kidmirage/CHESSmate-Reproduction/Firmware/CHESSmate_ESP32/cpu.c

/** CHESSmate emulator for Arduino.
 *
 *  Most of this is the 6502 emulator from Mike Chambers.
 *
 *    http://forum.arduino.cc/index.php?topic=193216.0
 *
 *  Project inspired by Oscar Vermeulen's KIM-1 Uno project.
 *
 *    https://obsolescence.wixsite.com/obsolescence/kim-uno-summary-c1uuh
 *
 *  CHESSmate code added by Michael Gardi.
 *
 *    https://hackaday.io/project/194011-commodore-chessmate-reproduction
 *
 */

#include <stdint.h>

extern uint8_t readRRIOT(uint16_t address);
extern void writeRRIOT(uint16_t address, uint8_t value);
extern void printhex(uint16_t val);
extern void print_instruction(char r_w, uint16_t pc, uint16_t address, uint8_t val);
    

#define NULL (void *) 0

#define CHESSMATE_ROM 0xF000
#define RRIOT_REGISTERS 0x8B00
#define RRIOT_RAM_ADDR 0x8B80
#define RRIOT_ROM_ADDR 0x8C00

#define RAM_SIZE 1536
#define ROM_SIZE 4096
#define RRIOT_REG_SIZE 16
#define RRIOT_RAM_SIZE 64
#define RRIOT_ROM_SIZE 1024

//6502 defines
#define UNDOCUMENTED //when this is defined, undocumented opcodes are handled.
                     //otherwise, they're simply treated as NOPs.

#define USE_TIMING //slower, but allows you to specify number of cycles to run for exec6502
                   //rather than simply a number of instructions. also uses a little more
                   //program memory when enabled.

#define FLAG_CARRY     0x01
#define FLAG_ZERO      0x02
#define FLAG_INTERRUPT 0x04
#define FLAG_DECIMAL   0x08
#define FLAG_BREAK     0x10
#define FLAG_CONSTANT  0x20
#define FLAG_OVERFLOW  0x40
#define FLAG_SIGN      0x80

#define BASE_STACK     0x100

#define saveaccum(n) a = (uint8_t)((n) & 0x00FF)


//flag modifier macros
#define setcarry() cpustatus |= FLAG_CARRY
#define clearcarry() cpustatus &= (~FLAG_CARRY)
#define setzero() cpustatus |= FLAG_ZERO
#define clearzero() cpustatus &= (~FLAG_ZERO)
#define setinterrupt() cpustatus |= FLAG_INTERRUPT
#define clearinterrupt() cpustatus &= (~FLAG_INTERRUPT)
#define setdecimal() cpustatus |= FLAG_DECIMAL
#define cleardecimal() cpustatus &= (~FLAG_DECIMAL)
#define setoverflow() cpustatus |= FLAG_OVERFLOW
#define clearoverflow() cpustatus &= (~FLAG_OVERFLOW)
#define setsign() cpustatus |= FLAG_SIGN
#define clearsign() cpustatus &= (~FLAG_SIGN)


//flag calculation macros
#define zerocalc(n) { if ((n) & 0x00FF) clearzero(); else setzero(); }

#define signcalc(n) { if ((n) & 0x0080) setsign(); else clearsign(); }

#define carrycalc(n) { if ((n) & 0xFF00) setcarry(); else clearcarry(); }

#define overflowcalc(n, m, o) { if (((n) ^ (uint16_t)(m)) & ((n) ^ (o)) & 0x0080) setoverflow(); else clearoverflow(); }


//6502 CPU registers
uint16_t pc;
uint8_t sp, a, x, y, cpustatus;
// BCD fix OV 20140915 - helper variables for adc and sbc
uint16_t lxx,hxx;
// end of BCD fix part 1


//helper variables
uint32_t instructions = 0; //keep track of total instructions executed
int32_t clockticks6502 = 0, clockgoal6502 = 0;
uint16_t oldpc, ea, reladdr, value, result;
uint8_t opcode, oldcpustatus, useaccum;

uint16_t getpc() {
  return(pc);
}

uint8_t getop() {
  return(opcode);
}

uint8_t RAM[RAM_SIZE];

uint8_t const CHESSMATE[ROM_SIZE] = {
  0xd8, 0x58, 0xa2, 0xfe, 0x9a, 0xa9, 0x3f, 0x8d, 0x03, 0x8b, 0xa9, 0xff, 0xa2, 0x00, 0x95, 0x00,
  0xd5, 0x00, 0xf0, 0x05, 0xb5, 0x00, 0x4c, 0x14, 0xf0, 0xca, 0xd0, 0xf2, 0x49, 0xff, 0xf0, 0xee,
  0xa9, 0x05, 0x85, 0x53, 0xa2, 0x21, 0xbd, 0x52, 0xfe, 0x95, 0x00, 0xca, 0x10, 0xf8, 0x86, 0x59,
  0x20, 0xf0, 0xf2, 0xa9, 0x70, 0x85, 0x56, 0xa9, 0x20, 0x20, 0x9c, 0xff, 0x38, 0xe9, 0x04, 0xd0,
  0xf8, 0xa2, 0x04, 0x4c, 0x60, 0xf2, 0xa9, 0xee, 0x85, 0x83, 0x85, 0x84, 0xd8, 0xa2, 0xfe, 0x9a,
  0xa2, 0xb8, 0x86, 0x61, 0xa5, 0x78, 0x29, 0x88, 0x24, 0x56, 0x70, 0x02, 0x09, 0x10, 0x85, 0x78,
  0xa2, 0x00, 0x38, 0x20, 0x04, 0xff, 0xc9, 0x0a, 0xd0, 0x03, 0x4c, 0xb9, 0xf0, 0xc9, 0x09, 0xf0,
  0xd5, 0xe0, 0x04, 0x30, 0x02, 0xa2, 0x00, 0xe0, 0x00, 0xd0, 0x04, 0x86, 0x83, 0x86, 0x84, 0x20,
  0x85, 0xf0, 0x4c, 0x62, 0xf0, 0xe0, 0x03, 0xf0, 0x16, 0xe0, 0x02, 0xf0, 0x0e, 0xe0, 0x01, 0xf0,
  0x04, 0x0a, 0x0a, 0x0a, 0x0a, 0x05, 0x83, 0x85, 0x83, 0xe8, 0x60, 0x0a, 0x0a, 0x0a, 0x0a, 0x05,
  0x84, 0x85, 0x84, 0xe8, 0x60, 0xa9, 0x00, 0x85, 0x7c, 0x85, 0x7d, 0x85, 0x7e, 0xa9, 0xf5, 0x8d,
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
	  return (CHESSMATE[PGMaddr]);
  }

  // RAM memory.
  if (address < RAM_SIZE) return(RAM[address]);

  // Check for RRIOT registers.
  if (address >= RRIOT_REGISTERS && address < (RRIOT_REGISTERS + RRIOT_REG_SIZE)) {
	  PGMaddr = address - RRIOT_REGISTERS;
	  return readRRIOT(PGMaddr);
  }

  // Check for RRIOT RAM.
  if (address >= RRIOT_RAM_ADDR && address < (RRIOT_RAM_ADDR + RRIOT_RAM_SIZE)) {
	  PGMaddr = address - RRIOT_RAM_ADDR;
  	return(RRIOT_RAM[PGMaddr]);
  }

  // Check for OPENING_BOOK.
  if (address >= RRIOT_ROM_ADDR && address < (RRIOT_ROM_ADDR + RRIOT_ROM_SIZE)) {
    PGMaddr = address - RRIOT_ROM_ADDR;
    return(OPENING_BOOK[PGMaddr]);
  }

  // Should have no effect on the program.
  if (address == 0x8009) {
    return 0x00;
  }

  // Catch any unhandled reads.
  uint16_t showpc = getpc();
  print_instruction('r',showpc,address,0);
  return 0xFF;
}

void write6502(uint16_t address, uint8_t value) {
  uint16_t PGMaddr;

  if (address < RAM_SIZE) {
    RAM[address] = value;
    return;
  }

  // Check for RRIOT registers.
  if (address >= RRIOT_REGISTERS && address < (RRIOT_REGISTERS + RRIOT_REG_SIZE)) {
	  PGMaddr = address - RRIOT_REGISTERS;
	  writeRRIOT(PGMaddr, value);
    return;
  }

  // Check for RRIOT RAM.
  if (address >= RRIOT_RAM_ADDR && address < (RRIOT_RAM_ADDR + RRIOT_RAM_SIZE)) {
  	  PGMaddr = address - RRIOT_RAM_ADDR;
      RRIOT_RAM[PGMaddr] = value;
      return;
  }
  // Catch any unhandled writes.
  uint16_t showpc = getpc();
  print_instruction('w',showpc,address, value);
}

//a few general functions used by various other functions
void push16(uint16_t pushval) {
    write6502(BASE_STACK + sp, (pushval >> 8) & 0xFF);
    write6502(BASE_STACK + ((sp - 1) & 0xFF), pushval & 0xFF);
    sp -= 2;
}

void push8(uint8_t pushval) {
    write6502(BASE_STACK + sp--, pushval);
}

uint16_t pull16() {
    uint16_t temp16;
    temp16 = read6502(BASE_STACK + ((sp + 1) & 0xFF)) | ((uint16_t)read6502(BASE_STACK + ((sp + 2) & 0xFF)) << 8);
    sp += 2;
    return(temp16);
}

uint8_t pull8() {
    return (read6502(BASE_STACK + ++sp));
}

void reset6502() {
    pc = (uint16_t)read6502(0xFFFC) | ((uint16_t)read6502(0xFFFD) << 8);
    a = 0;
    x = 0;
    y = 0;
    sp = 0xFD;
    cpustatus |= FLAG_CONSTANT;
}

//addressing mode functions, calculates effective addresses
void imp() { //implied
}

void acc() { //accumulator
  useaccum = 1;
}

void imm() { //immediate
    ea = pc++;
}

void zp() { //zero-page
    ea = (uint16_t)read6502((uint16_t)pc++);
}

void zpx() { //zero-page,X
    ea = ((uint16_t)read6502((uint16_t)pc++) + (uint16_t)x) & 0xFF; //zero-page wraparound
}

void zpy() { //zero-page,Y
    ea = ((uint16_t)read6502((uint16_t)pc++) + (uint16_t)y) & 0xFF; //zero-page wraparound
}

void rel() { //relative for branch ops (8-bit immediate value, sign-extended)
    reladdr = (uint16_t)read6502(pc++);
    if (reladdr & 0x80) reladdr |= 0xFF00;
}

void abso() { //absolute
    ea = (uint16_t)read6502(pc) | ((uint16_t)read6502(pc+1) << 8);
    pc += 2;
}

void absx() { //absolute,X
    uint16_t startpage;
    ea = ((uint16_t)read6502(pc) | ((uint16_t)read6502(pc+1) << 8));
    startpage = ea & 0xFF00;
    ea += (uint16_t)x;

    pc += 2;
}

void absy() { //absolute,Y
    uint16_t startpage;
    ea = ((uint16_t)read6502(pc) | ((uint16_t)read6502(pc+1) << 8));
    startpage = ea & 0xFF00;
    ea += (uint16_t)y;

    pc += 2;
}

void ind() { //indirect
    uint16_t eahelp, eahelp2;
    eahelp = (uint16_t)read6502(pc) | (uint16_t)((uint16_t)read6502(pc+1) << 8);
    eahelp2 = (eahelp & 0xFF00) | ((eahelp + 1) & 0x00FF); //replicate 6502 page-boundary wraparound bug
    ea = (uint16_t)read6502(eahelp) | ((uint16_t)read6502(eahelp2) << 8);
    pc += 2;
}

void indx() { // (indirect,X)
    uint16_t eahelp;
    eahelp = (uint16_t)(((uint16_t)read6502(pc++) + (uint16_t)x) & 0xFF); //zero-page wraparound for table pointer
    ea = (uint16_t)read6502(eahelp & 0x00FF) | ((uint16_t)read6502((eahelp+1) & 0x00FF) << 8);
}

void indy() { // (indirect),Y
    uint16_t eahelp, eahelp2, startpage;
    eahelp = (uint16_t)read6502(pc++);
    eahelp2 = (eahelp & 0xFF00) | ((eahelp + 1) & 0x00FF); //zero-page wraparound
    ea = (uint16_t)read6502(eahelp) | ((uint16_t)read6502(eahelp2) << 8);
    startpage = ea & 0xFF00;
    ea += (uint16_t)y;

}

static uint16_t getvalue() {
    if (useaccum) return((uint16_t)a);
        else return((uint16_t)read6502(ea));
}

static uint16_t getvalue16() {
    return((uint16_t)read6502(ea) | ((uint16_t)read6502(ea+1) << 8));
}

void putvalue(uint16_t saveval) {
    if (useaccum) a = (uint8_t)(saveval & 0x00FF);
        else write6502(ea, (saveval & 0x00FF));
}


//instruction handler functions
void adc() {
    // penaltyop = 1;
    value = getvalue();
    result = (uint16_t)a + value + (uint16_t)(cpustatus & FLAG_CARRY);

    zerocalc(result);
    overflowcalc(result, a, value);
    signcalc(result);

    #ifndef NES_CPU
    if (cpustatus & FLAG_DECIMAL)       /* detect and apply BCD nybble carries */
        result += ((((result + 0x66) ^ (uint16_t)a ^ value) >> 3) & 0x22) * 3;
    #endif

    carrycalc(result);
    saveaccum(result);

    saveaccum(result);
}

void op_and() {
    value = getvalue();
    result = (uint16_t)a & value;

    zerocalc(result);
    signcalc(result);

    saveaccum(result);
}

void asl() {
    value = getvalue();
    result = value << 1;

    carrycalc(result);
    zerocalc(result);
    signcalc(result);

    putvalue(result);
}

void bcc() {
    if ((cpustatus & FLAG_CARRY) == 0) {
        oldpc = pc;
        pc += reladdr;
        if ((oldpc & 0xFF00) != (pc & 0xFF00)) clockticks6502 += 2; //check if jump crossed a page boundary
            else clockticks6502++;
    }
}

void bcs() {
    if ((cpustatus & FLAG_CARRY) == FLAG_CARRY) {
        oldpc = pc;
        pc += reladdr;
        if ((oldpc & 0xFF00) != (pc & 0xFF00)) clockticks6502 += 2; //check if jump crossed a page boundary
            else clockticks6502++;
    }
}

void beq() {
    if ((cpustatus & FLAG_ZERO) == FLAG_ZERO) {
        oldpc = pc;
        pc += reladdr;
        if ((oldpc & 0xFF00) != (pc & 0xFF00)) clockticks6502 += 2; //check if jump crossed a page boundary
            else clockticks6502++;
    }
}

void op_bit() {
    value = getvalue();
    result = (uint16_t)a & value;

    zerocalc(result);
    cpustatus = (cpustatus & 0x3F) | (uint8_t)(value & 0xC0);
}

void bmi() {
    if ((cpustatus & FLAG_SIGN) == FLAG_SIGN) {
        oldpc = pc;
        pc += reladdr;
        if ((oldpc & 0xFF00) != (pc & 0xFF00)) clockticks6502 += 2; //check if jump crossed a page boundary
            else clockticks6502++;
    }
}

void bne() {
    if ((cpustatus & FLAG_ZERO) == 0) {
        oldpc = pc;
        pc += reladdr;
        if ((oldpc & 0xFF00) != (pc & 0xFF00)) clockticks6502 += 2; //check if jump crossed a page boundary
            else clockticks6502++;
    }
}

void bpl() {
    if ((cpustatus & FLAG_SIGN) == 0) {
        oldpc = pc;
        pc += reladdr;
        if ((oldpc & 0xFF00) != (pc & 0xFF00)) clockticks6502 += 2; //check if jump crossed a page boundary
            else clockticks6502++;
    }
}

void brk() {
    pc++;
    push16(pc); //push next instruction address onto stack
    push8(cpustatus | FLAG_BREAK); //push CPU cpustatus to stack
    setinterrupt(); //set interrupt flag
    pc = (uint16_t)read6502(0xFFFE) | ((uint16_t)read6502(0xFFFF) << 8);
}

void bvc() {
    if ((cpustatus & FLAG_OVERFLOW) == 0) {
        oldpc = pc;
        pc += reladdr;
        if ((oldpc & 0xFF00) != (pc & 0xFF00)) clockticks6502 += 2; //check if jump crossed a page boundary
            else clockticks6502++;
    }
}

void bvs() {
    if ((cpustatus & FLAG_OVERFLOW) == FLAG_OVERFLOW) {
        oldpc = pc;
        pc += reladdr;
        if ((oldpc & 0xFF00) != (pc & 0xFF00)) clockticks6502 += 2; //check if jump crossed a page boundary
            else clockticks6502++;
    }
}

void clc() {
    clearcarry();
}

void cld() {
    cleardecimal();
}

void cli() {
    clearinterrupt();
}

void clv() {
    clearoverflow();
}

void cmp() {
    value = getvalue();
    result = (uint16_t)a - value;

    if (a >= (uint8_t)(value & 0x00FF)) setcarry();
        else clearcarry();
    if (a == (uint8_t)(value & 0x00FF)) setzero();
        else clearzero();
    signcalc(result);
}

void cpx() {
    value = getvalue();
    result = (uint16_t)x - value;

    if (x >= (uint8_t)(value & 0x00FF)) setcarry();
        else clearcarry();
    if (x == (uint8_t)(value & 0x00FF)) setzero();
        else clearzero();
    signcalc(result);
}

void cpy() {
    value = getvalue();
    result = (uint16_t)y - value;

    if (y >= (uint8_t)(value & 0x00FF)) setcarry();
        else clearcarry();
    if (y == (uint8_t)(value & 0x00FF)) setzero();
        else clearzero();
    signcalc(result);
}

void dec() {
    value = getvalue();
    result = value - 1;

    zerocalc(result);
    signcalc(result);

    putvalue(result);
}

void dex() {
    x--;

    zerocalc(x);
    signcalc(x);
}

void dey() {
    y--;

    zerocalc(y);
    signcalc(y);
}

void eor() {
    value = getvalue();
    result = (uint16_t)a ^ value;

    zerocalc(result);
    signcalc(result);

    saveaccum(result);
}

void inc() {
    value = getvalue();
    result = value + 1;

    zerocalc(result);
    signcalc(result);

    putvalue(result);
}

void inx() {
    x++;

    zerocalc(x);
    signcalc(x);
}

void iny() {
    y++;

    zerocalc(y);
    signcalc(y);
}

void jmp() {
    pc = ea;
}

void jsr() {
    push16(pc - 1);
    pc = ea;
}

void lda() {
    value = getvalue();
    a = (uint8_t)(value & 0x00FF);

    zerocalc(a);
    signcalc(a);
}

void ldx() {
    value = getvalue();
    x = (uint8_t)(value & 0x00FF);

    zerocalc(x);
    signcalc(x);
}

void ldy() {
    value = getvalue();
    y = (uint8_t)(value & 0x00FF);

    zerocalc(y);
    signcalc(y);
}

void lsr() {
    value = getvalue();
    result = value >> 1;

    if (value & 1) setcarry();
        else clearcarry();
    zerocalc(result);
    signcalc(result);

    putvalue(result);
}

void nop() {
}

void ora() {
    value = getvalue();
    result = (uint16_t)a | value;

    zerocalc(result);
    signcalc(result);

    saveaccum(result);
}

void pha() {
    push8(a);
}

void php() {
    push8(cpustatus | FLAG_BREAK);
}

void pla() {
    a = pull8();

    zerocalc(a);
    signcalc(a);
}

void plp() {
    cpustatus = pull8() | FLAG_CONSTANT;
}

void rol() {
    value = getvalue();
    result = (value << 1) | (cpustatus & FLAG_CARRY);

    carrycalc(result);
    zerocalc(result);
    signcalc(result);

    putvalue(result);
}

void ror() {
    value = getvalue();
    result = (value >> 1) | ((cpustatus & FLAG_CARRY) << 7);

    if (value & 1) setcarry();
        else clearcarry();
    zerocalc(result);
    signcalc(result);

    putvalue(result);
}

void rti() {
    cpustatus = pull8();
    value = pull16();
    pc = value;
}

void rts() {
    value = pull16();
    pc = value + 1;
}

void sbc() {
    // penaltyop = 1;
    value = getvalue() ^ 0x00FF;     /* ones complement */

    #ifndef NES_CPU
    if (cpustatus & FLAG_DECIMAL)       /* use nines complement for BCD */
        value -= 0x0066;
    #endif

    result = (uint16_t)a + value + (uint16_t)(cpustatus & FLAG_CARRY);
   
    zerocalc(result);
    overflowcalc(result, a, value);
    signcalc(result);

    #ifndef NES_CPU
    if (cpustatus & FLAG_DECIMAL)       /* detect and apply BCD nybble carries */
        result += ((((result + 0x66) ^ (uint16_t)a ^ value) >> 3) & 0x22) * 3;
    #endif
   
    carrycalc(result);
    saveaccum(result);
}

void sec() {
    setcarry();
}

void sed() {
    setdecimal();
}

void sei() {
    setinterrupt();
}

void sta() {
    putvalue(a);
}

void stx() {
    putvalue(x);
}

void sty() {
    putvalue(y);
}

void tax() {
    x = a;

    zerocalc(x);
    signcalc(x);
}

void tay() {
    y = a;

    zerocalc(y);
    signcalc(y);
}

void tsx() {
    x = sp;

    zerocalc(x);
    signcalc(x);
}

void txa() {
    a = x;

    zerocalc(a);
    signcalc(a);
}

void txs() {
    sp = x;
}

void tya() {
    a = y;

    zerocalc(a);
    signcalc(a);
}

//undocumented instructions
#ifdef UNDOCUMENTED
    void lax() {
        lda();
        ldx();
    }

    void sax() {
        sta();
        stx();
        putvalue(a & x);
    }

    void dcp() {
        dec();
        cmp();
    }

    void isb() {
        inc();
        sbc();
    }

    void slo() {
        asl();
        ora();
    }

    void rla() {
        rol();
        op_and();
    }

    void sre() {
        lsr();
        eor();
    }

    void rra() {
        ror();
        adc();
    }
#else
    #define lax nop
    #define sax nop
    #define dcp nop
    #define isb nop
    #define slo nop
    #define rla nop
    #define sre nop
    #define rra nop
#endif


void nmi6502() {
    push16(pc);
    push8(cpustatus);
    cpustatus |= FLAG_INTERRUPT;
    pc = (uint16_t)read6502(0xFFFA) | ((uint16_t)read6502(0xFFFB) << 8);
}

void irq6502() {
    push16(pc);
    push8(cpustatus);
    cpustatus |= FLAG_INTERRUPT;
    pc = (uint16_t)read6502(0xFFFE) | ((uint16_t)read6502(0xFFFF) << 8);
}

#ifdef USE_TIMING
uint8_t const ticktable[256] = {
/*        |  0  |  1  |  2  |  3  |  4  |  5  |  6  |  7  |  8  |  9  |  A  |  B  |  C  |  D  |  E  |  F  |     */
/* 0 */      7,    6,    2,    8,    3,    3,    5,    5,    3,    2,    2,    2,    4,    4,    6,    6,  /* 0 */
/* 1 */      2,    5,    2,    8,    4,    4,    6,    6,    2,    4,    2,    7,    4,    4,    7,    7,  /* 1 */
/* 2 */      6,    6,    2,    8,    3,    3,    5,    5,    4,    2,    2,    2,    4,    4,    6,    6,  /* 2 */
/* 3 */      2,    5,    2,    8,    4,    4,    6,    6,    2,    4,    2,    7,    4,    4,    7,    7,  /* 3 */
/* 4 */      6,    6,    2,    8,    3,    3,    5,    5,    3,    2,    2,    2,    3,    4,    6,    6,  /* 4 */
/* 5 */      2,    5,    2,    8,    4,    4,    6,    6,    2,    4,    2,    7,    4,    4,    7,    7,  /* 5 */
/* 6 */      6,    6,    2,    8,    3,    3,    5,    5,    4,    2,    2,    2,    5,    4,    6,    6,  /* 6 */
/* 7 */      2,    5,    2,    8,    4,    4,    6,    6,    2,    4,    2,    7,    4,    4,    7,    7,  /* 7 */
/* 8 */      2,    6,    2,    6,    3,    3,    3,    3,    2,    2,    2,    2,    4,    4,    4,    4,  /* 8 */
/* 9 */      2,    6,    2,    6,    4,    4,    4,    4,    2,    5,    2,    5,    5,    5,    5,    5,  /* 9 */
/* A */      2,    6,    2,    6,    3,    3,    3,    3,    2,    2,    2,    2,    4,    4,    4,    4,  /* A */
/* B */      2,    5,    2,    5,    4,    4,    4,    4,    2,    4,    2,    4,    4,    4,    4,    4,  /* B */
/* C */      2,    6,    2,    8,    3,    3,    5,    5,    2,    2,    2,    2,    4,    4,    6,    6,  /* C */
/* D */      2,    5,    2,    8,    4,    4,    6,    6,    2,    4,    2,    7,    4,    4,    7,    7,  /* D */
/* E */      2,    6,    2,    8,    3,    3,    5,    5,    2,    2,    2,    2,    4,    4,    6,    6,  /* E */
/* F */      2,    5,    2,    8,    4,    4,    6,    6,    2,    4,    2,    7,    4,    4,    7,    7   /* F */
};
#endif

void exec6502(int32_t tickcount) {
#ifdef USE_TIMING
  clockgoal6502 += tickcount;

  while (clockgoal6502 > 0) {
#else
  while (tickcount--) {
#endif
    opcode = read6502(pc++);
    cpustatus |= FLAG_CONSTANT;

    useaccum = 0;

		switch (opcode) {
		case 0x0:
			imp();
			brk();
			break;
		case 0x1:
			indx();
			ora();
			break;
		case 0x5:
			zp();
			ora();
			break;
		case 0x6:
			zp();
			asl();
			break;
		case 0x8:
			imp();
			php();
			break;
		case 0x9:
			imm();
			ora();
			break;
		case 0xA:
			acc();
			asl();
			break;
		case 0xD:
			abso();
			ora();
			break;
		case 0xE:
			abso();
			asl();
			break;
		case 0x10:
			rel();
			bpl();
			break;
		case 0x11:
			indy();
			ora();
			break;
		case 0x15:
			zpx();
			ora();
			break;
		case 0x16:
			zpx();
			asl();
			break;
		case 0x18:
			imp();
			clc();
			break;
		case 0x19:
			absy();
			ora();
			break;
		case 0x1D:
			absx();
			ora();
			break;
		case 0x1E:
			absx();
			asl();
			break;
		case 0x20:
			abso();
			jsr();
			break;
		case 0x21:
			indx();
			op_and();
			break;
		case 0x24:
			zp();
			op_bit();
			break;
		case 0x25:
			zp();
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
		case 0xC6:
			zp();
			dec();
			break;
		case 0xC8:
			imp();
			iny();
			break;
		case 0xC9:
			imm();
			cmp();
			break;
		case 0xCA:
			imp();
			dex();
			break;
		case 0xCC:
			abso();
			cpy();
			break;
		case 0xCD:
			abso();
			cmp();
			break;
		case 0xCE:
			abso();
			dec();
			break;
		case 0xD0:
			rel();
			bne();
			break;
		case 0xD1:
			indy();
			cmp();
			break;
		case 0xD5:
			zpx();
			cmp();
			break;
		case 0xD6:
			zpx();
			dec();
			break;
		case 0xD8:
			imp();
			cld();
			break;
		case 0xD9:
			absy();
			cmp();
			break;
		case 0xDD:
			absx();
			cmp();
			break;
		case 0xDE:
			absx();
			dec();
			break;
		case 0xE0:
			imm();
			cpx();
			break;
		case 0xE1:
			indx();
			sbc();
			break;
		case 0xE4:
			zp();
			cpx();
			break;
		case 0xE5:
			zp();
			sbc();
			break;
		case 0xE6:
			zp();
			inc();
			break;
		case 0xE8:
			imp();
			inx();
			break;
		case 0xE9:
			imm();
			sbc();
			break;
		case 0xEB:
			imm();
			sbc();
			break;
		case 0xEC:
			abso();
			cpx();
			break;
		case 0xED:
			abso();
			sbc();
			break;
		case 0xEE:
			abso();
			inc();
			break;
		case 0xF0:
			rel();
			beq();
			break;
		case 0xF1:
			indy();
			sbc();
			break;
		case 0xF5:
			zpx();
			sbc();
			break;
		case 0xF6:
			zpx();
			inc();
			break;
		case 0xF8:
			imp();
			sed();
			break;
		case 0xF9:
			absy();
			sbc();
			break;
		case 0xFD:
			absx();
			sbc();
			break;
		case 0xFE:
			absx();
			inc();
			break;
		}
#ifdef USE_TIMING
      clockgoal6502 -= ticktable[opcode];
#endif
      instructions++;
  }
}
